thunderkeys/StealthFork/STLs/Panels/Salad Fork Rear Panel Conversion/[a]_Bowden_Tube_Entry_Accent_Cover_x1.stl

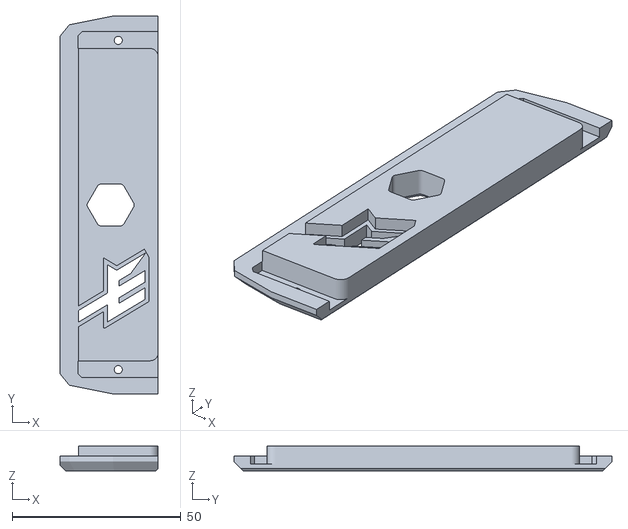
[picture p18: CAD file, 2025-03-27]
STLs/Panels/Salad Fork Rear Panel Conversion/[a]_Bowden_Tube_Entry_Accent_Cover_x1.stl
29.2 x 112.1 x 7.40
