thunderkeys/StealthFork/STLs/Skirts/160/160_Corner_A_Front_Skirt _x1.stl

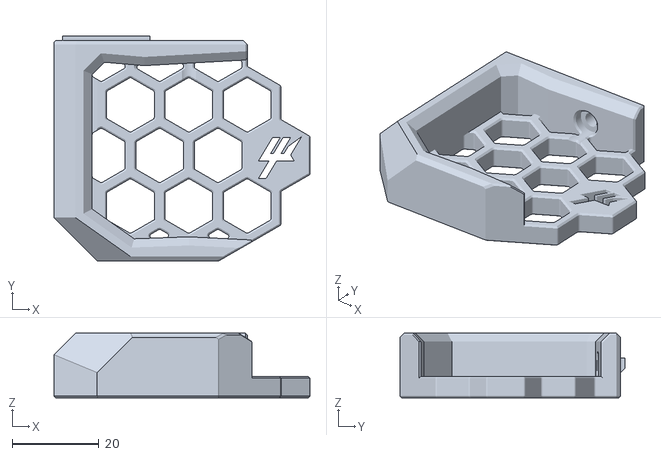
[picture p19: CAD file, 2025-03-15]
STLs/Skirts/160/160_Corner_A_Front_Skirt _x1.stl
59.2 x 52.0 x 15.0
