thunderkeys/StealthFork/STLs/Skirts/180/[a]_Corner_B_Side_Skirt_Accent_x2.stl

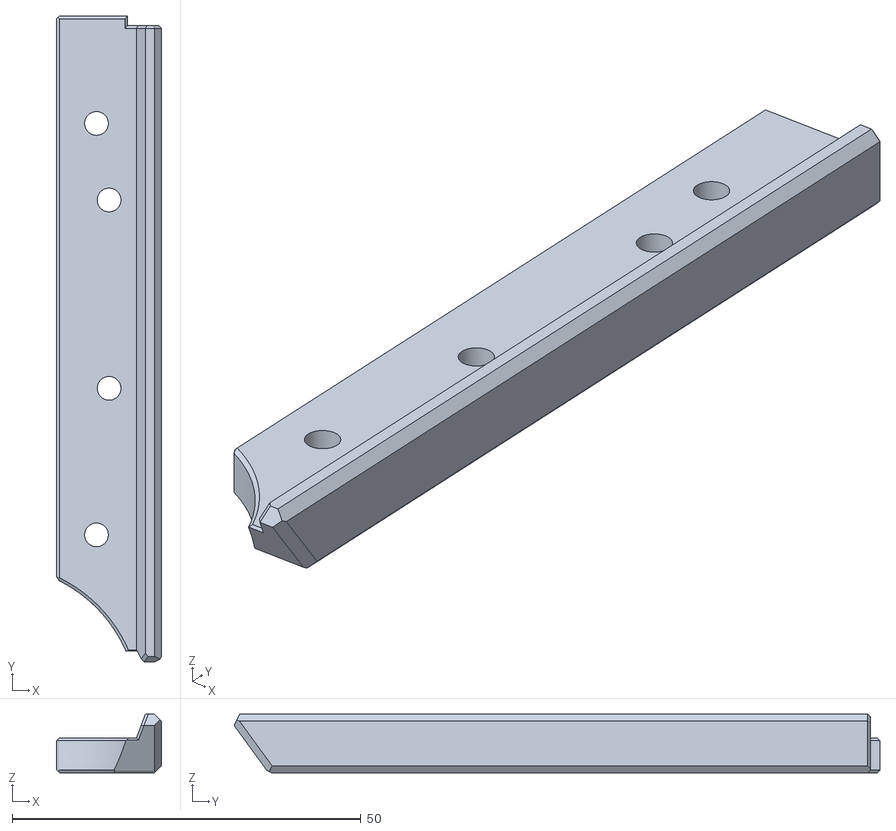
[picture p20: CAD file, 2025-03-11]
STLs/Skirts/180/[a]_Corner_B_Side_Skirt_Accent_x2.stl
15.0 x 92.6 x 8.40
