thunderkeys/StealthFork/STLs/Skirts/Common STLs/Corner_B_Foot_Mount_x2.stl

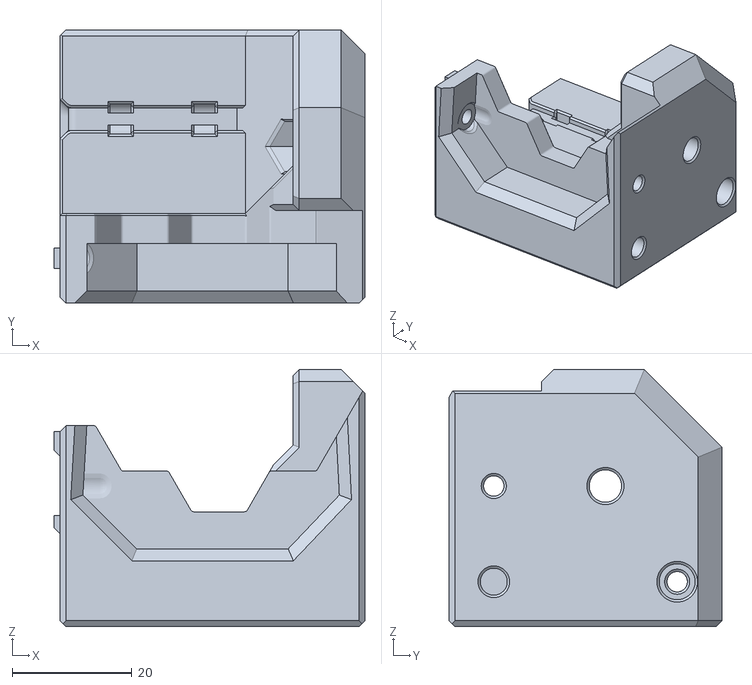
[picture p21: CAD file, 2025-03-11]
STLs/Skirts/Common STLs/Corner_B_Foot_Mount_x2.stl
52.0 x 45.7 x 43.0
