thunderkeys/StealthFork/STLs/Panels/Salad Fork Rear Panel Conversion/Bowden Tube Entry Rear Cover Base_x1.stl

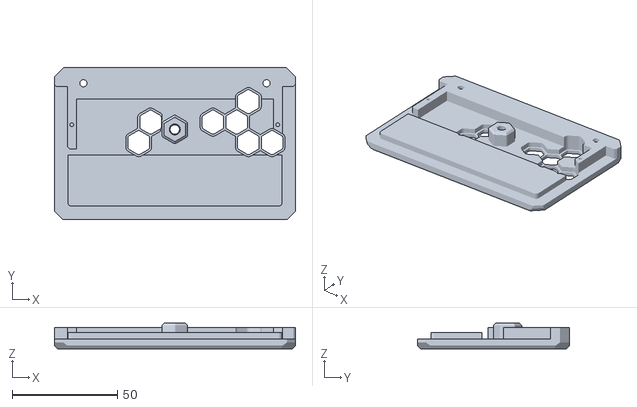
[picture p22: CAD file, 2025-03-27]
STLs/Panels/Salad Fork Rear Panel Conversion/Bowden Tube Entry Rear Cover Base_x1.stl
114.2 x 72.1 x 12.1
