thunderkeys/StealthFork/STLs/Skirts/160/160_Corner_A_Side_Skirt_x2.stl

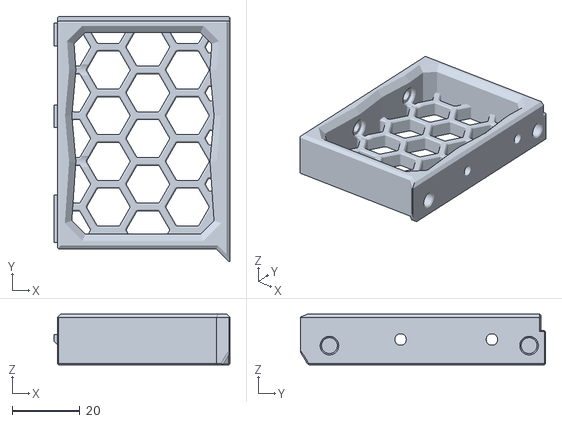
[picture p23: CAD file, 2025-03-15]
STLs/Skirts/160/160_Corner_A_Side_Skirt_x2.stl
52.0 x 72.5 x 15.0
