thunderkeys/StealthFork/STLs/Skirts/180/[a]_Rear_Skirt_Accent_x1.stl

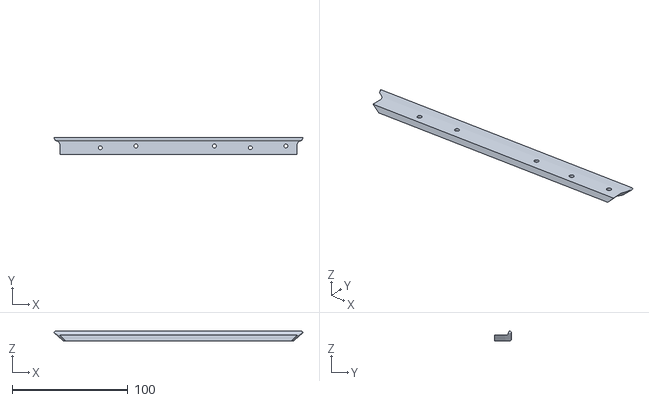
[picture p24: CAD file, 2025-03-11]
STLs/Skirts/180/[a]_Rear_Skirt_Accent_x1.stl
215.2 x 15.0 x 8.40
