thunderkeys/StealthFork/STLs/Skirts/Common STLs/[a]_Centre_Fan_Grill_Insert_x2.stl

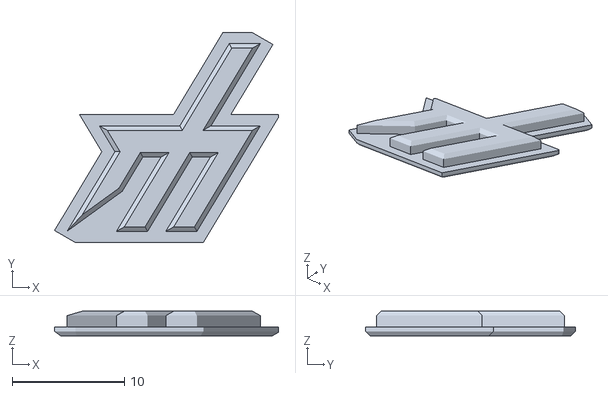
[picture p25: CAD file, 2025-03-11]
STLs/Skirts/Common STLs/[a]_Centre_Fan_Grill_Insert_x2.stl
20.0 x 18.8 x 2.20
