thunderkeys/StealthFork/STLs/Z/[a]_Z_Carriage_Accent_Right_x1.stl

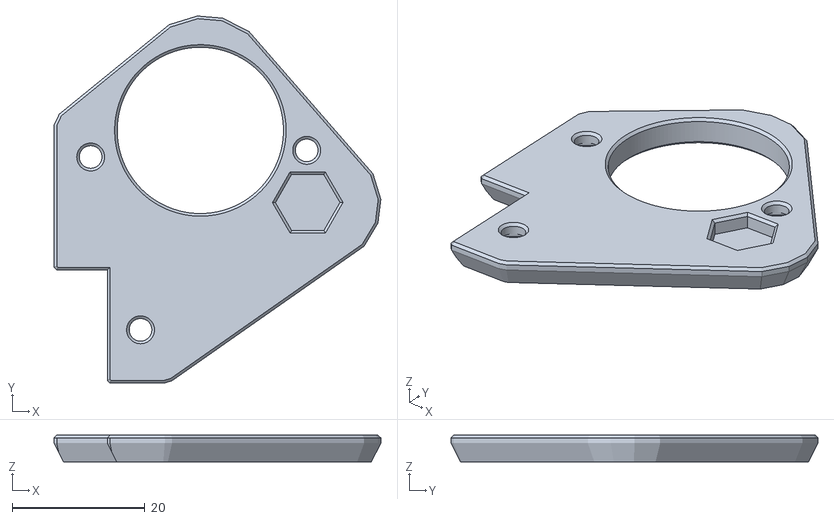
[picture p26: CAD file, 2025-03-11]
STLs/Z/[a]_Z_Carriage_Accent_Right_x1.stl
49.2 x 55.2 x 4.00
