thunderkeys/StealthFork/STLs/Panels/[a]_Bowden_Tube_Entry_Accent_Coverx1.stl

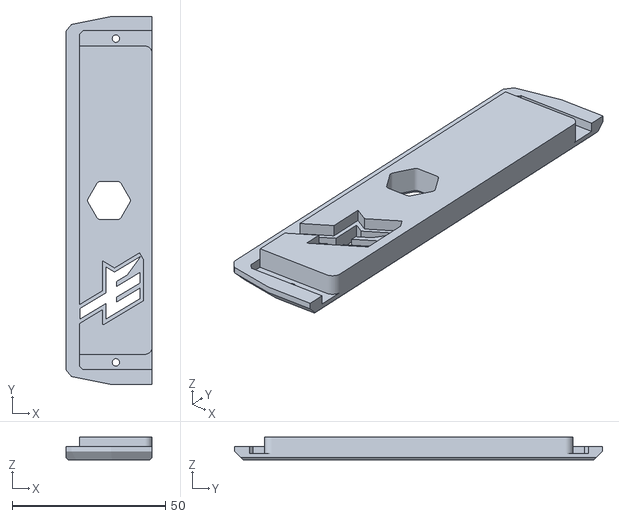
[picture p27: CAD file, 2025-03-11]
STLs/Panels/[a]_Bowden_Tube_Entry_Accent_Coverx1.stl
28.2 x 120.1 x 7.40
