thunderkeys/StealthFork/STLs/Panels/Salad Fork Rear Panel Conversion/[a]_Hex_Insert_A_x1.stl

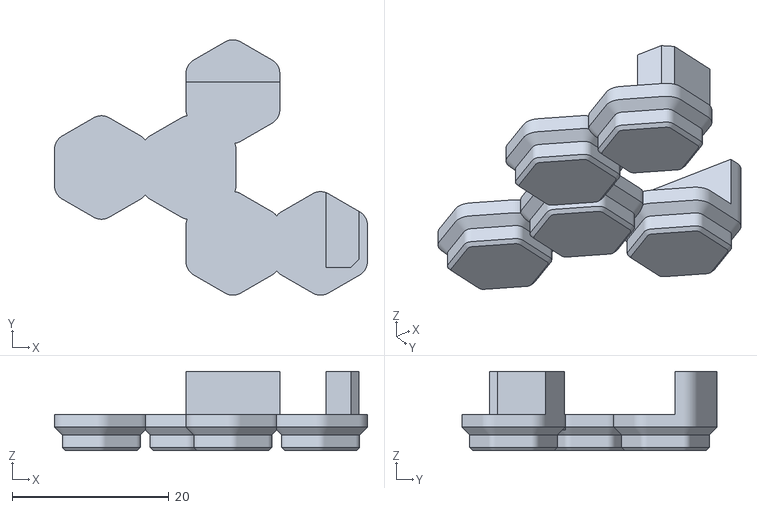
[picture p28: CAD file, 2025-03-27]
STLs/Panels/Salad Fork Rear Panel Conversion/[a]_Hex_Insert_A_x1.stl
40.0 x 32.6 x 10.1
