thunderkeys/StealthFork/STLs/Skirts/180/Corner_A_Front_Skirt_x1.stl

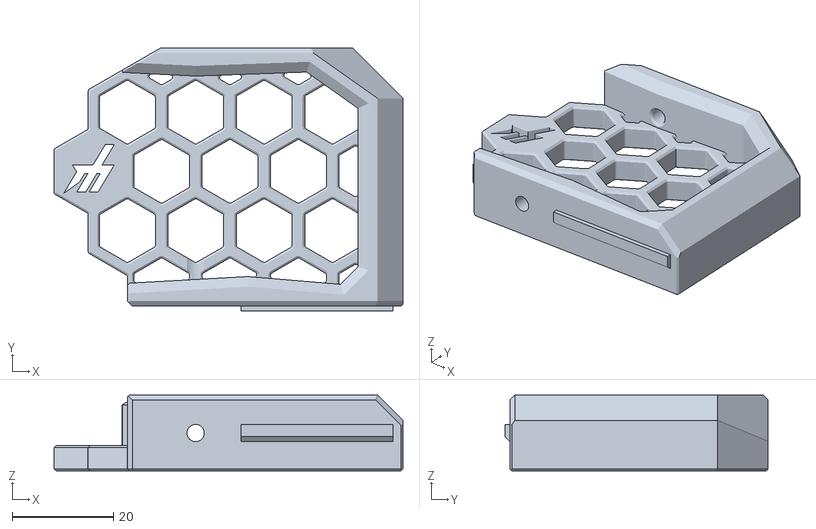
[picture p29: CAD file, 2025-03-11]
STLs/Skirts/180/Corner_A_Front_Skirt_x1.stl
68.9 x 52.0 x 15.0
