thunderkeys/StealthFork/STLs/Skirts/Common STLs/Adamstech_Inlet_Skirt_x1.stl

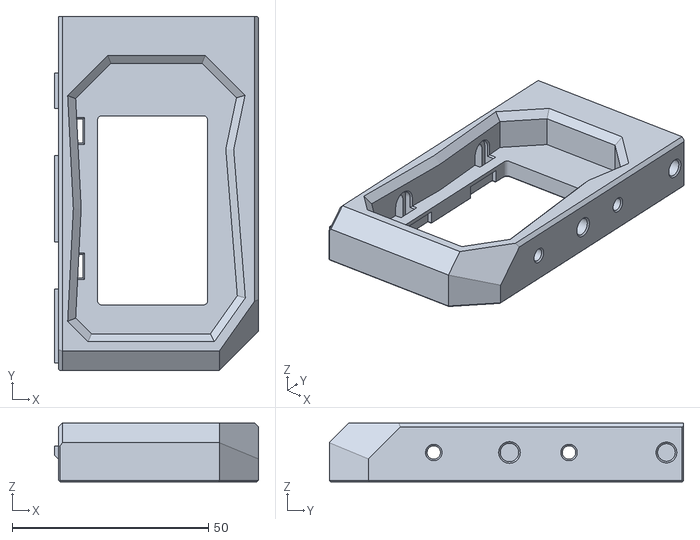
[picture p30: CAD file, 2025-03-11]
STLs/Skirts/Common STLs/Adamstech_Inlet_Skirt_x1.stl
52.0 x 90.3 x 15.0
