thunderkeys/StealthFork/STLs/Panels/Top_Hinge_Leaf_x1.stl

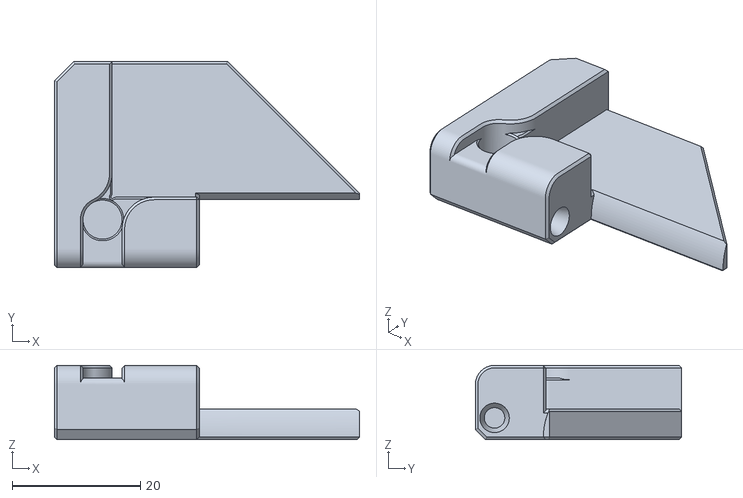
[picture p32: CAD file, 2025-03-11]
STLs/Panels/Top_Hinge_Leaf_x1.stl
47.6 x 32.2 x 11.6
