thunderkeys/StealthFork/STLs/Skirts/160/[a]_160_Corner_A_Foot_Mount_Accent_x1.stl

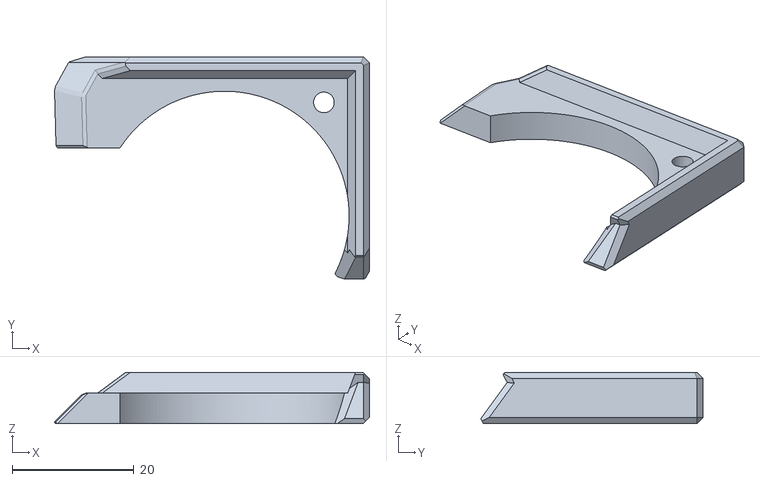
[picture p33: CAD file, 2025-03-15]
STLs/Skirts/160/[a]_160_Corner_A_Foot_Mount_Accent_x1.stl
51.8 x 36.6 x 8.40
