thunderkeys/StealthFork/STLs/Skirts/180/Corner_A_Side_Skirt_x2.stl

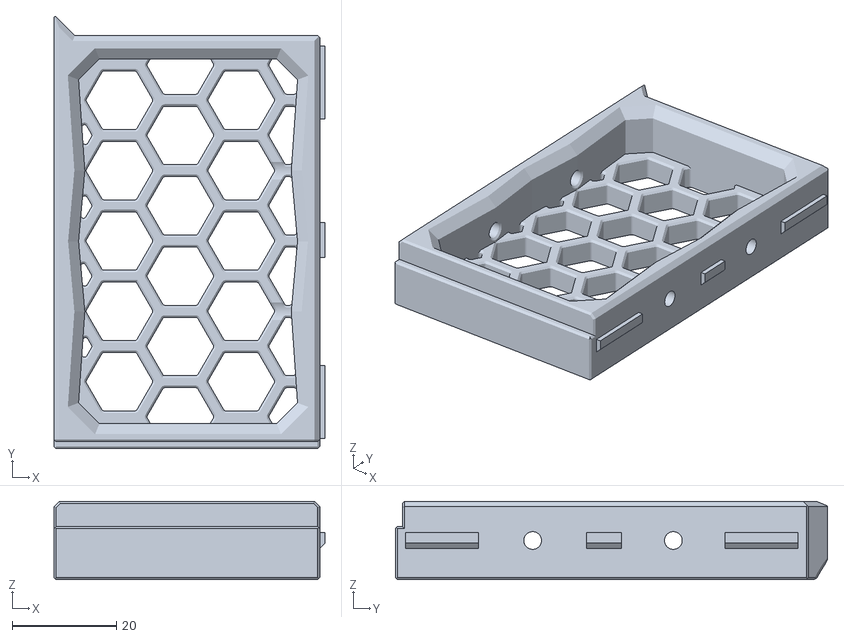
[picture p34: CAD file, 2025-03-11]
STLs/Skirts/180/Corner_A_Side_Skirt_x2.stl
52.0 x 83.0 x 15.0
