thunderkeys/StealthFork/STLs/Skirts/Common STLs/[a]_StealthFork_Waveshare43_Bezel_x1.stl

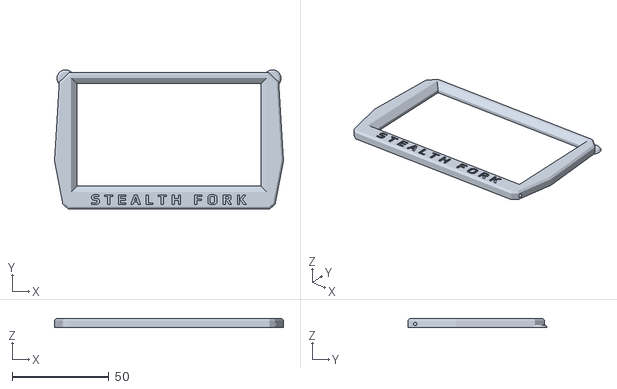
[picture p35: CAD file, 2025-03-11]
STLs/Skirts/Common STLs/[a]_StealthFork_Waveshare43_Bezel_x1.stl
118.3 x 72.0 x 4.65
