thunderkeys/StealthFork/STLs/Z/[a]_Z_Bracket_Left_x1.stl

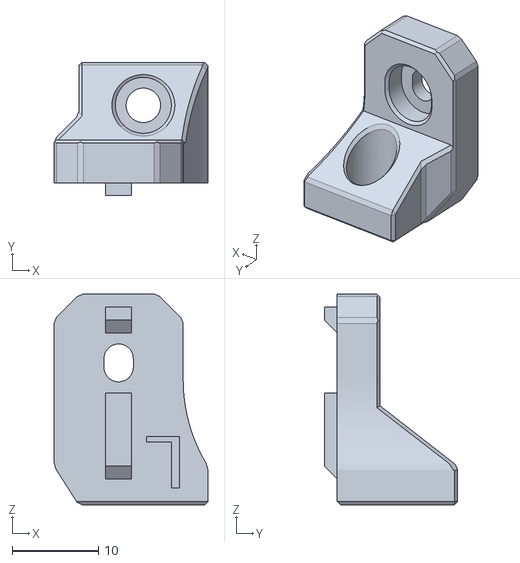
[picture p36: CAD file, 2025-03-11]
STLs/Z/[a]_Z_Bracket_Left_x1.stl
17.9 x 15.5 x 24.5
