thunderkeys/StealthFork/STLs/Gantry/A_B_Drives/A_Drive_Frame_Upper_Pinned.stl

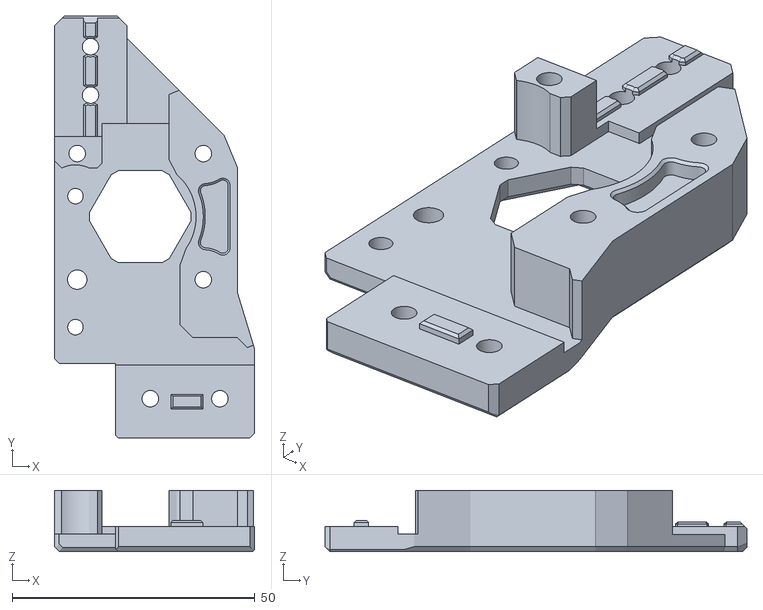
[picture p37: CAD file, 2025-03-11]
STLs/Gantry/A_B_Drives/A_Drive_Frame_Upper_Pinned.stl
41.3 x 87.0 x 12.6
