thunderkeys/StealthFork/STLs/Panels/Top_Hinge_Leaf_MMU_x1.3mf

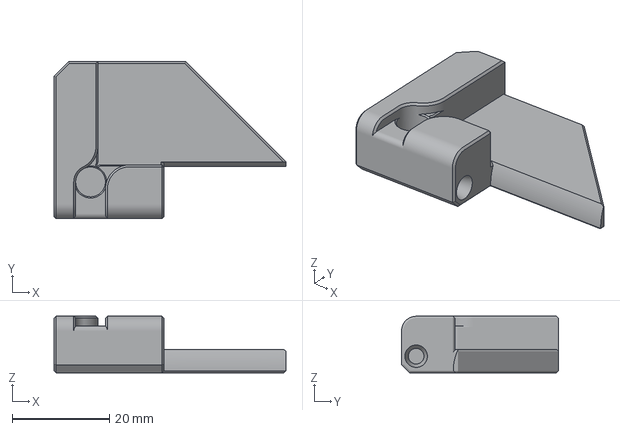
[picture p38: CAD file, 2025-03-11]
STLs/Panels/Top_Hinge_Leaf_MMU_x1.3mf
47.6 x 32.2 x 11.6 mm
