thunderkeys/StealthFork/STLs/Skirts/160/[a]_160_Corner_A_Side_Skirt_Accent_x2.stl

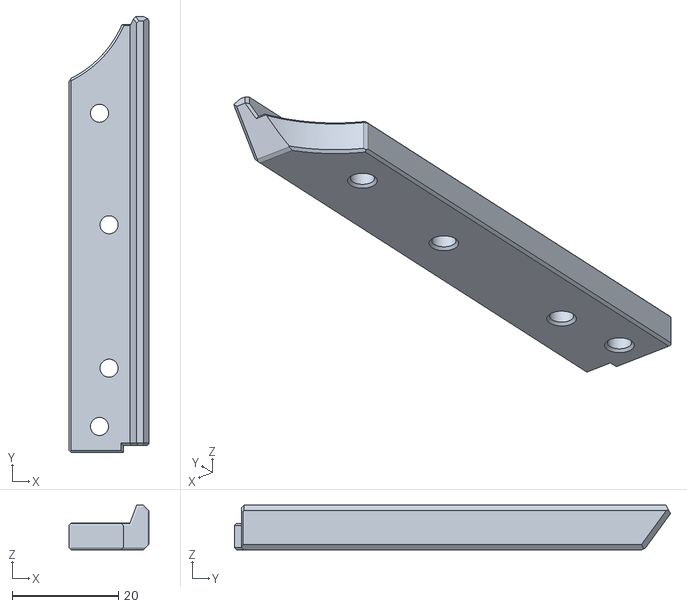
[picture p39: CAD file, 2025-03-15]
STLs/Skirts/160/[a]_160_Corner_A_Side_Skirt_Accent_x2.stl
15.0 x 82.1 x 8.40
