thunderkeys/StealthFork/STLs/Skirts/Common STLs/Power_Inlet_Corner_Foot_Mount_x1.stl

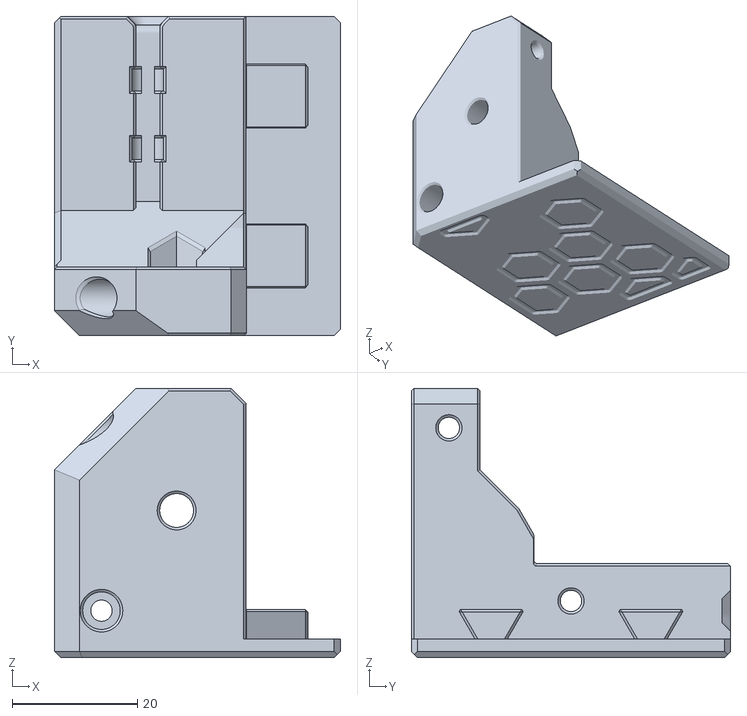
[picture p40: CAD file, 2025-03-11]
STLs/Skirts/Common STLs/Power_Inlet_Corner_Foot_Mount_x1.stl
45.7 x 51.0 x 43.0
