thunderkeys/StealthFork/STLs/Z/Z_Motor_Mount_Insert_x3.stl

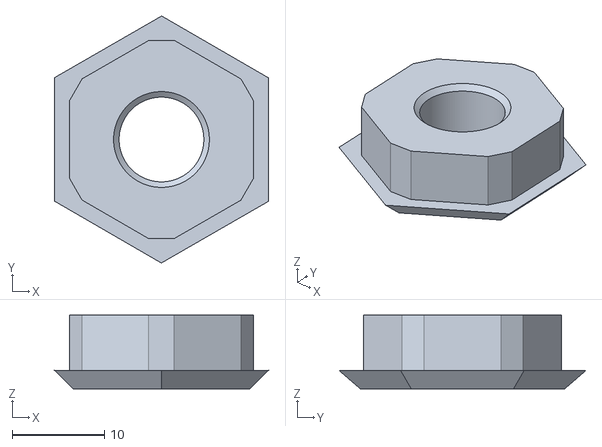
[picture p41: CAD file, 2025-03-11]
STLs/Z/Z_Motor_Mount_Insert_x3.stl
23.2 x 26.8 x 8.00
