thunderkeys/StealthFork/STLs/Panels/Salad Fork Rear Panel Conversion/[a]_Hex_Insert_B_x1.stl

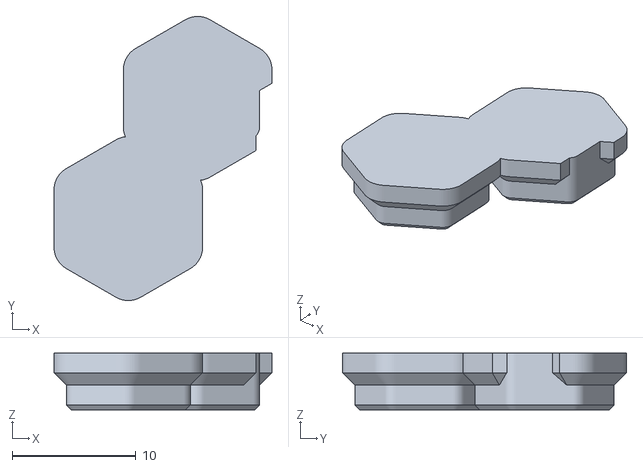
[picture p42: CAD file, 2025-03-27]
STLs/Panels/Salad Fork Rear Panel Conversion/[a]_Hex_Insert_B_x1.stl
17.6 x 22.9 x 4.60
