thunderkeys/StealthFork/STLs/Skirts/180/[a]_Corner_B_Foot_Mount_Accent_x2.stl

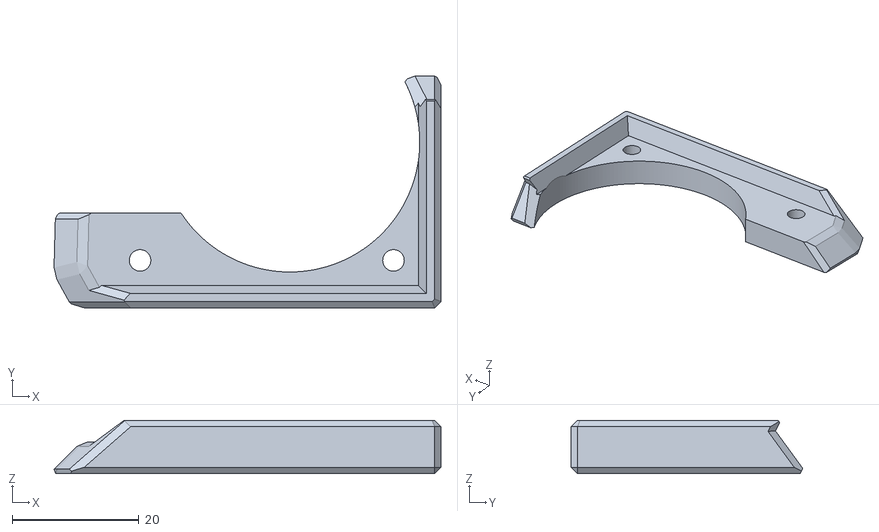
[picture p43: CAD file, 2025-03-11]
STLs/Skirts/180/[a]_Corner_B_Foot_Mount_Accent_x2.stl
61.1 x 36.6 x 8.40
