thunderkeys/StealthFork/STLs/Skirts/Common STLs/[a]_Centre_Skirt_Accent_x2.stl

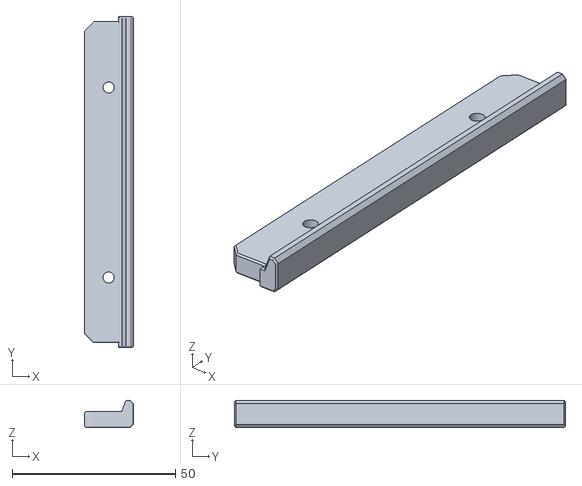
[picture p44: CAD file, 2025-03-11]
STLs/Skirts/Common STLs/[a]_Centre_Skirt_Accent_x2.stl
15.0 x 101.5 x 8.40
