thunderkeys/StealthFork/STLs/Z/[a]_Z_Motor_Mount_Rear_x1.stl

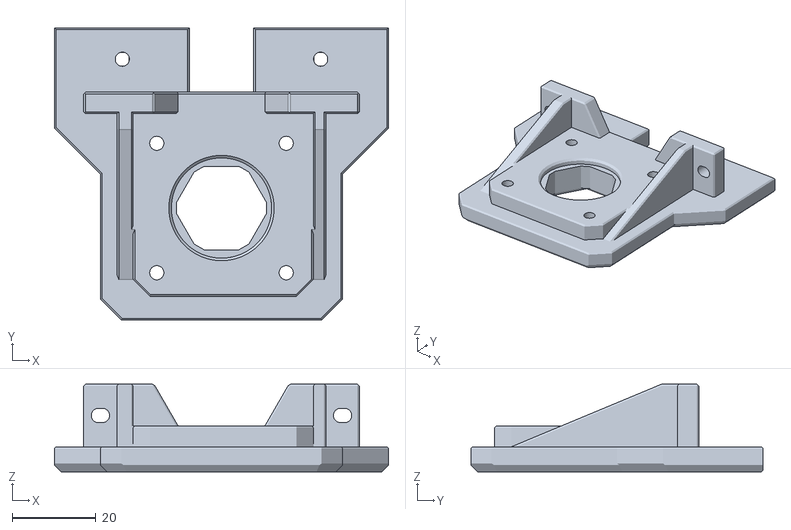
[picture p45: CAD file, 2025-03-11]
STLs/Z/[a]_Z_Motor_Mount_Rear_x1.stl
80.0 x 70.0 x 21.0
