thunderkeys/StealthFork/STLs/Skirts/160/[a]_160_Rear_Skirt_Accent_x1.stl

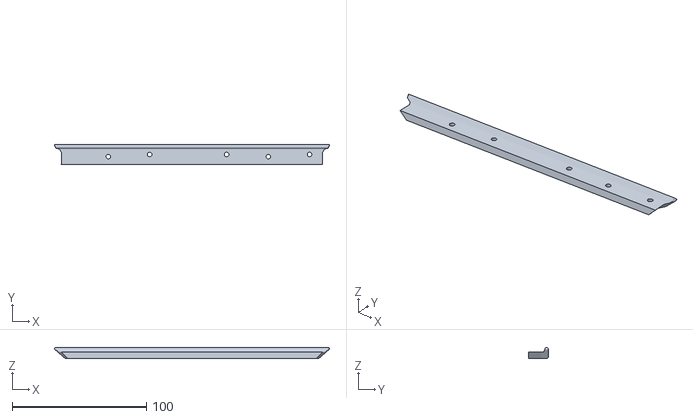
[picture p46: CAD file, 2025-03-15]
STLs/Skirts/160/[a]_160_Rear_Skirt_Accent_x1.stl
204.7 x 15.0 x 8.40
