thunderkeys/StealthFork/STLs/Skirts/Common STLs/[a]_StealthFork_TFT35_Bezel_x1.stl

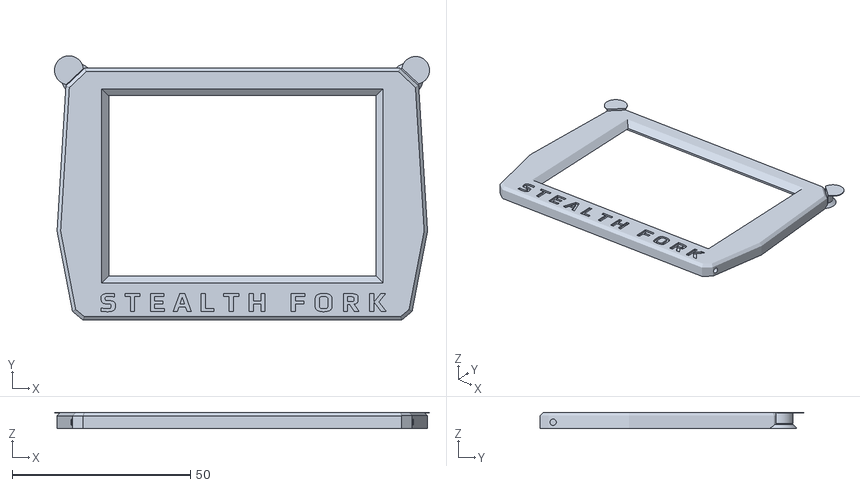
[picture p47: CAD file, 2025-03-11]
STLs/Skirts/Common STLs/[a]_StealthFork_TFT35_Bezel_x1.stl
105.1 x 74.1 x 4.60
