thunderkeys/StealthFork/STLs/Z/[a]_Z_Motor_Mount_Right_x1.stl

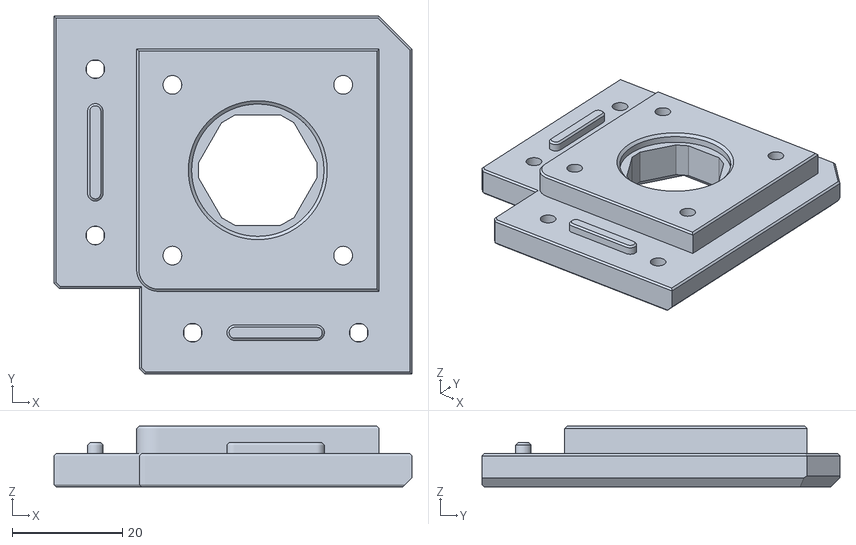
[picture p48: CAD file, 2025-03-11]
STLs/Z/[a]_Z_Motor_Mount_Right_x1.stl
65.0 x 65.0 x 11.0
