thunderkeys/StealthFork/STLs/Skirts/Common STLs/[a]_Skirt_Logo_Insert_x3.stl

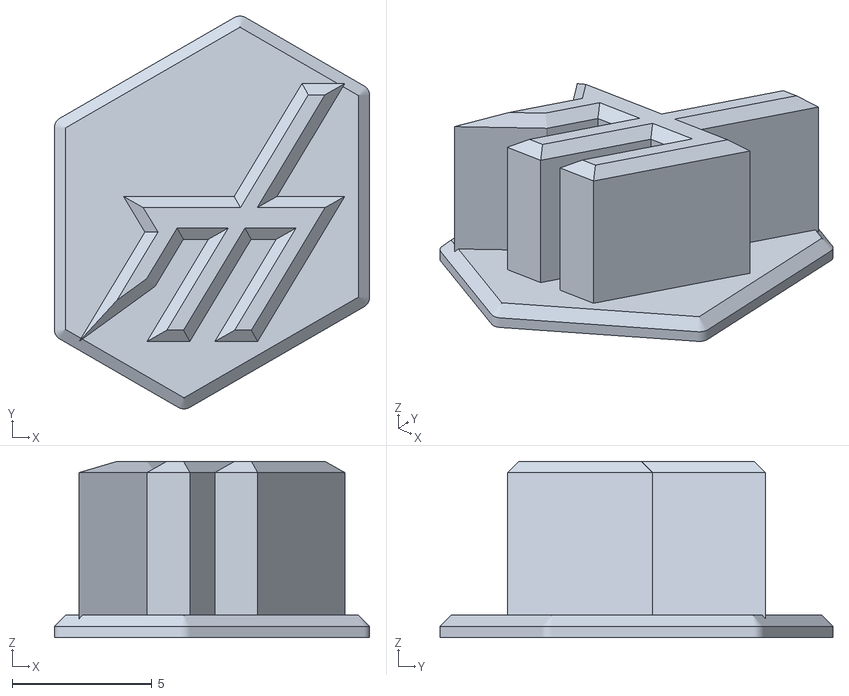
[picture p49: CAD file, 2025-03-11]
STLs/Skirts/Common STLs/[a]_Skirt_Logo_Insert_x3.stl
11.3 x 14.0 x 6.30
