thunderkeys/StealthFork/STLs/Skirts/Common STLs/Centre_Fan_Grill_x2.stl

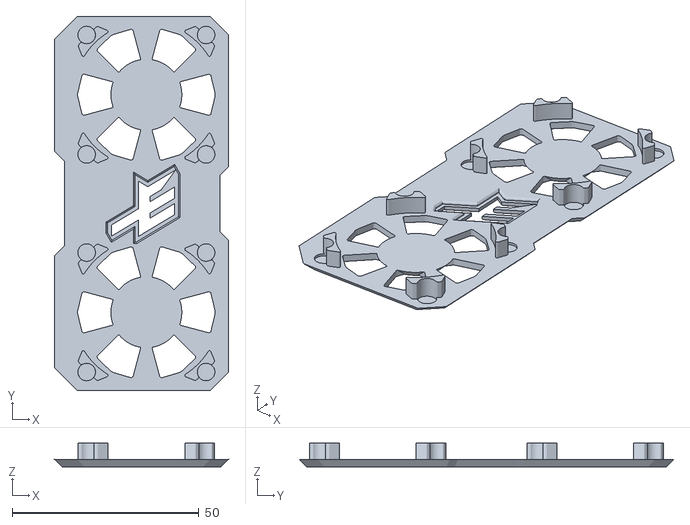
[picture p50: CAD file, 2025-03-11]
STLs/Skirts/Common STLs/Centre_Fan_Grill_x2.stl
46.6 x 100.3 x 6.40
