thunderkeys/StealthFork/STLs/Z/[a]_Z_Chain_Anchor_Deck_x1.stl

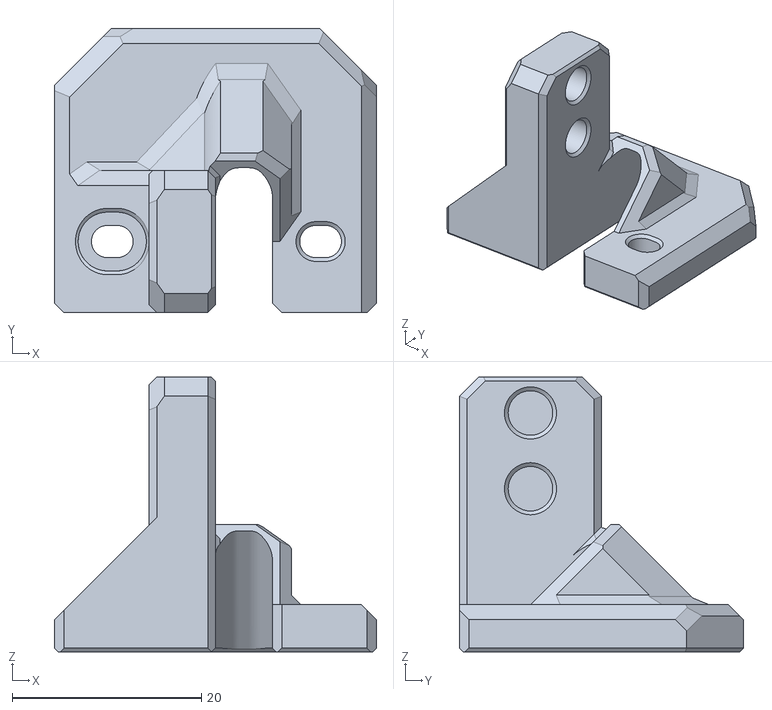
[picture p51: CAD file, 2025-03-11]
STLs/Z/[a]_Z_Chain_Anchor_Deck_x1.stl
34.0 x 30.0 x 29.0
