thunderkeys/StealthFork/STLs/Z/[a]_Z_Bed_Mount_Rear_x1.stl

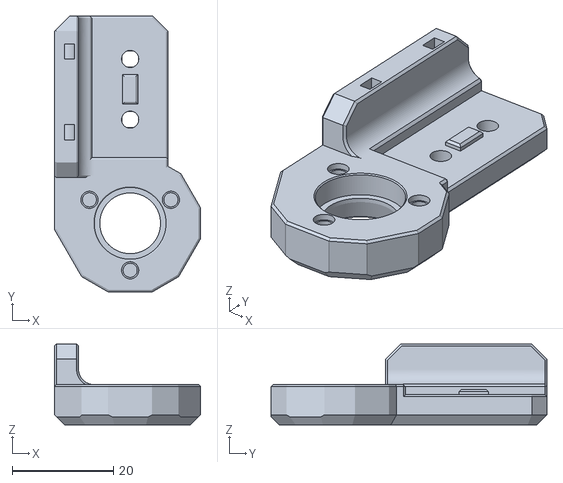
[picture p52: CAD file, 2025-03-11]
STLs/Z/[a]_Z_Bed_Mount_Rear_x1.stl
28.9 x 54.6 x 16.0
