thunderkeys/StealthFork/STLs/Z/[a]_Z_Carriage_Accent_Rear_x1.stl

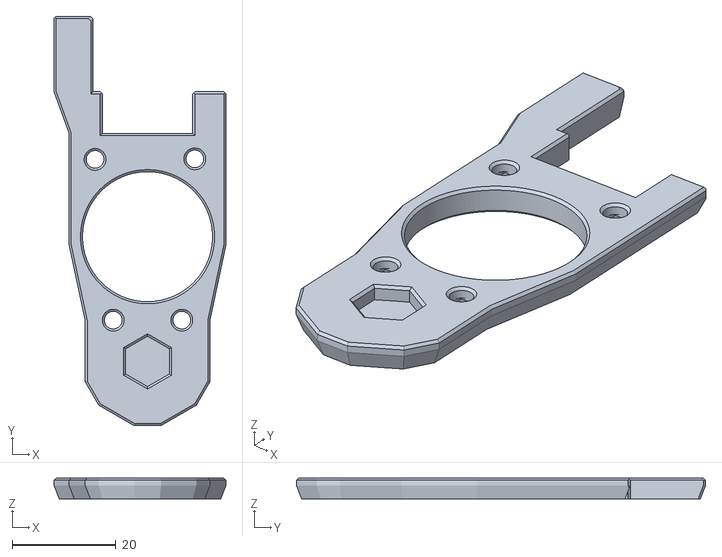
[picture p53: CAD file, 2025-03-11]
STLs/Z/[a]_Z_Carriage_Accent_Rear_x1.stl
33.1 x 78.8 x 4.00
